scarlet-snake/Color-Clock-v2/pictures/1319.jpg

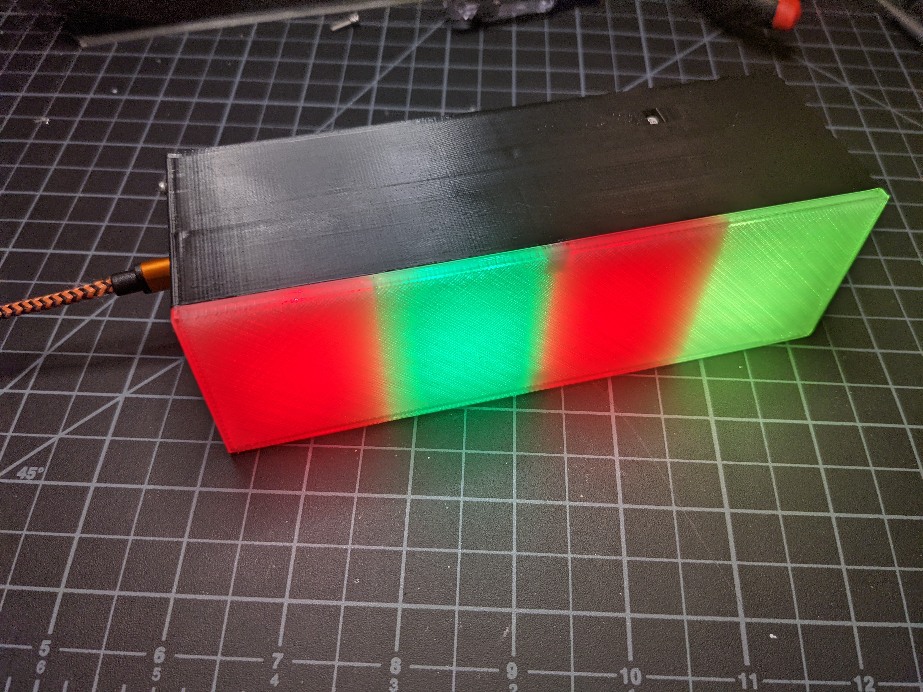
pictures/1319.jpg
