scarlet-snake/Color-Clock-v2/pictures/1334.jpg

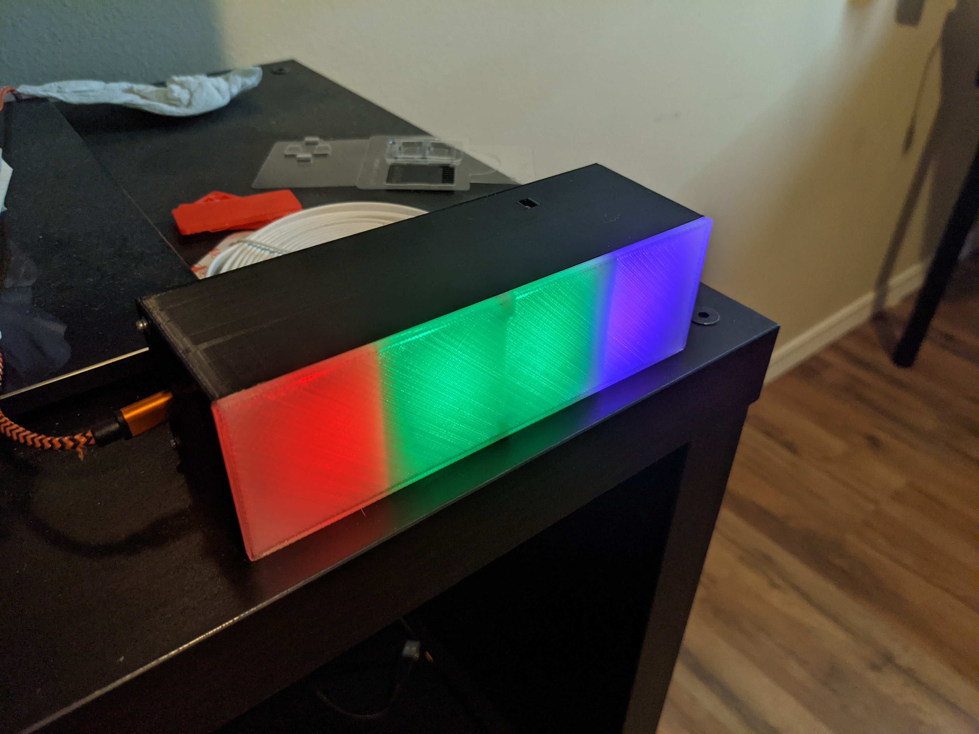
pictures/1334.jpg
