scarlet-snake/Color-Clock-v2/pictures/1600.jpg

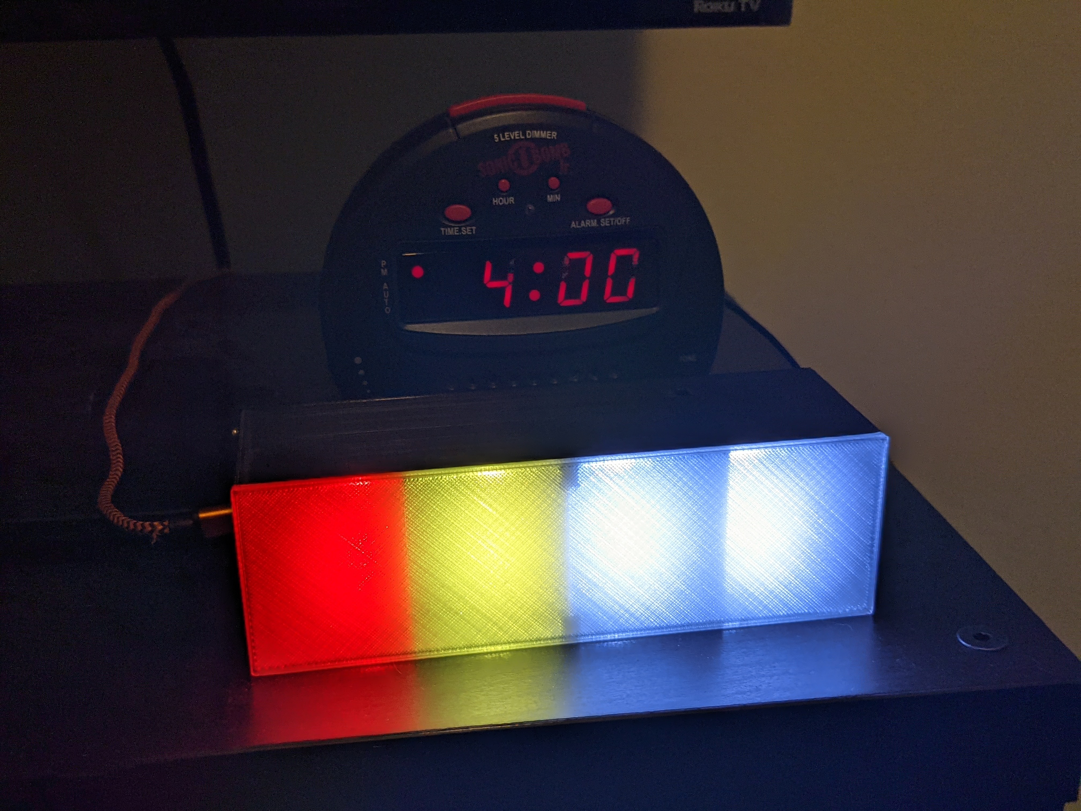
pictures/1600.jpg
