scarlet-snake/Color-Clock-v2/pictures/1608-1609.gif

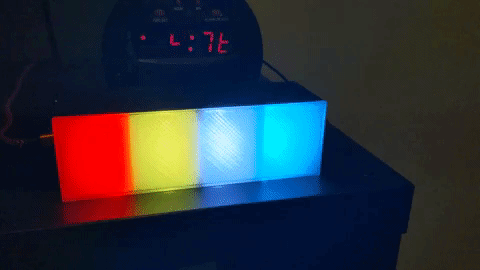
pictures/1608-1609.gif
