scarlet-snake/Color-Clock-v2/pictures/Version 1/PXL_20210410_024621346.jpg

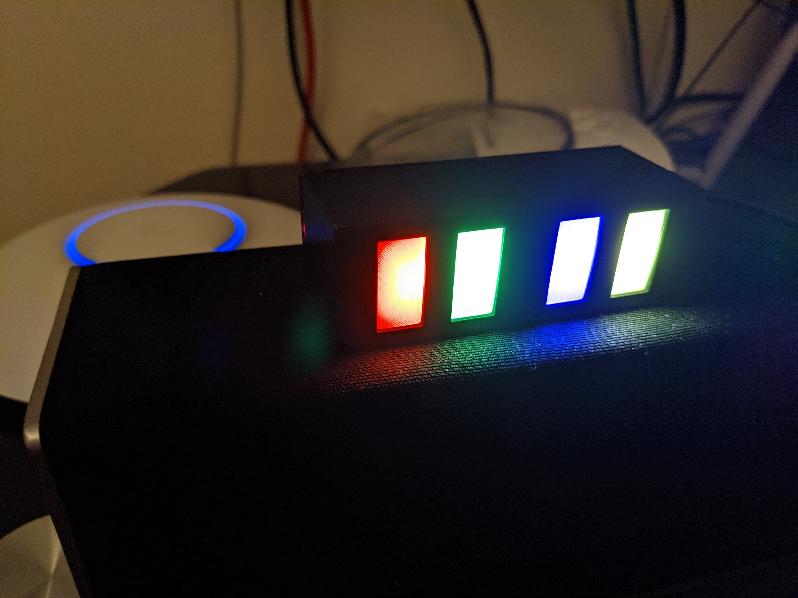
pictures/Version 1/PXL_20210410_024621346.jpg
