scarlet-snake/Color-Clock-v2/pictures/Version 1/PXL_20210410_024628636.jpg

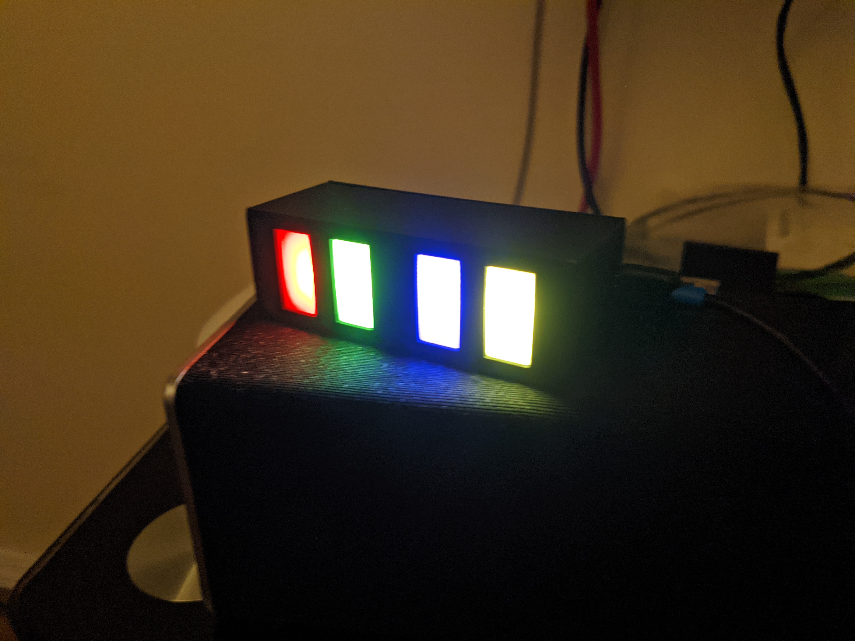
pictures/Version 1/PXL_20210410_024628636.jpg
